ikatkov/dummy-load/ltspice/darlington-bjt-current-measurement.asc

C1: cap; 100p
Q1: npn; 2SCR583D3
Q3: npn; 2SC5866
R1: res; 1k
R2: res; 50
R3: res; 0.23
R4: res; 0.1
R5: res; 1k
R6: res; 9.1k
U1: opamp2; LM358
U2: opamp2; LM358
V1: voltage; 24
V2: voltage; 0
V3: voltage; 7
V5: voltage; {Von}; AC 0
Named nets: 0, RAW, VCC, -VCC, ref, sense, Vmes
.param Von=0.5
.inc LM358.LIB
.tran 0 100u 20u
