ikatkov/dummy-load/ltspice/PWM_example_usage.asc

X1: PWM_Gen; DutyCycle=1 PWM_V=3.3 PWM_f=50k
X2: PWM_Gen; DutyCycle={DutyCycle2} PWM_V=3.3 PWM_f=50k
X3: PWM_Gen; DutyCycle={DutyCycle3} PWM_V=PWM3_V PWM_f=PWM3_f
Named nets: my_pwm1, my_pwm2, my_pwm3
.tran 0.0005
.param DutyCycle2=40
.param DutyCycle3=75
PWM Signal Generator - Example Usage
J.Kincell June 2021
CurrentSauce.co.uk
Example 1. All parameters are set within.
i.e. Right Click component, add the PARAMS as shown here.
(Tick the check box so it apprears in sch)
Example 2. Some parameters are set within.
The duty cycle is set via an 'external' .PARAM placed within the schematic.
Allows multiple instantiations of different PWM sources
.param PWM3_V=5
.param PWM3_f=25k
Example 3. All parameters set by external .PARAM statement
When doing this, is clearer to not display the component PARAMS.
i.e. Untick the checkbox after right clicking)
Put the "PWM_Gen.asy" and "PWM_Gen.asc" in the top-level of a simulation project.
When adding a component, at the top, change the "top-level" drop-down box from the
default directory to the project directory, and there you will find the "PWM_Gen" component.
