ikatkov/dummy-load/ltspice/temp-measurement-scale.asc

R1: res; 25k
R8: res; 25k
R9: res; 5k
R10: res; 5k
U2: opamp2; LM358
V1: voltage; 7
V2: voltage; 2
V3: voltage; PWL(0 2 1m 2 2m 2.5 3m 2.5 4m 2.9)
Named nets: 0, vcc, volt-divider-scaled, v-ref
.lib LM358.lib
.tran 10m uic
