ikatkov/dummy-load/ltspice/temp-measurement.asc

R6: res; 51k
R7: res; 4.7k
R8: res; 4.7k
R9: res; 51k
R10: res; R=1k*(0.0002*temp*temp+0.0537*temp+8.5256)
R11: res; 10k
R12: res; 10k
R13: res; 10k
U2: opamp2; LM358
U3: opamp2; LM358
V1: voltage; 2
V2: voltage; 4.55
V3: voltage; 7
Named nets: 0, v-ref, vcc, volt-divider-scaled, 2V
.dc temp 0 120 1
~2.275V
2.09V ~0C
2.90V ~120C
2.09V ~0C
2.90V ~120C
.lib LM358.lib
