ikatkov/dummy-load/ltspice/voltage-measurement.asc

C1: cap; 10µ
D1: diode
D2: diode
R2: res; 25.5k
R3: res; 100k
V1: voltage; PWL(0 4 1 24 4 24 4.001 0)
V2: voltage; 5
V3: voltage; SINE(0 0.25 60)
Named nets: 0, vref, 5V
.tran 0 10 0
LSB = 23mV
10b ADC
