ikatkov/dummy-load/ltspice/LM334/LM334_test.asc

C6: cap; 100n
D1: diode; 1N4148
R1: res; 500; tol=0.1 pwr=0.1
R2: res; 5k; tol=0.1 pwr=0.1
R4: res; 10k; tol=0.001 pwr=0.010
U1: LM334
V3: voltage; 5V
Named nets: 0
.STEP TEMP  27 77
.op
Iset = 227uV*T/R1
Iset = 0.0681V/R @27°C, 300K
The LM334 should be normally used for currents >=10uA.
R2=10*R1 is recommended
for temperature compensation
