ikatkov/dummy-load/ltspice/bjt-stability-pulse.asc

C1: cap; 100p
C2: cap; 2.2µ
L1: ind; 3µ
Q1: npn; TIP122
R1: res; 10k
R2: res; 1m
R3: res; 0.23
R4: res; 0.1
R5: res; 1
U1: opamp2; LM358
V1: voltage; 5
V2: voltage; -5
V3: voltage; 5
V4: voltage; PULSE({0.001 - Von} 0 100n 100n 100n 1m); AC 0
V5: voltage; {Von}; AC 0
Named nets: 0, RAW, VCC, fb, out, -VCC, ref
;ac dec 1000 1 100Meg
.inc TLV271.LIB
.inc LM358.LIB
.tran 100u
.param Von=0.01
.lib TIP122.LIB
