ikatkov/dummy-load/ltspice/bjt-stability.asc

C2: cap; 100p
C3: cap; 2.2µ
L1: ind; 3µ
Q1: npn; 2SC5824
Q2: npn; 2N3904
R1: res; 1
R3: res; 0.23
R4: res; 100
R6: res; 10k
U1: opamp2; LM358
V1: voltage; 5
V2: voltage; -5
V3: voltage; 5
V4: voltage; ""; AC 1
V5: voltage; {Von}; AC 0
Named nets: 0, RAW, VCC, fb, -VCC, ref, inv
.ac dec 1000 1 10Meg
.inc TLV271.LIB
.inc LM358.LIB
;tran 500ms
.lib TIP122.LIB
.param Von=0.25
