ikatkov/dummy-load/ltspice/current-sense-multiplier.asc

R1: res; 1k
R2: res; 9.1k
U1: opamp2; LM358
V1: voltage; 48
V2: voltage; 7
V3: voltage; 0
V4: voltage; {Von}; AC 0
Named nets: VCC, -VCC, 0, Vmes, ref, RAW
.param Von=0.4
.inc LM358.LIB
.tran 100m
