ikatkov/dummy-load/ltspice/darlington-bjt-high-side-mes.asc

C1: cap; 220p
C2: cap; 2.2µ
L1: ind; 3µ
Q1: npn; 2SCR583D3
Q3: npn; 2SC5866
R1: res; 1k
R2: res; 47
R3: res; 1
R4: res; 0.1
R5: res; 3.3
R6: res; 10k
R7: res; 1
R8: res; 1k
R9: res; 0.215
U1: opamp2; LM358
U2: opamp2; LM358
V1: voltage; 60
V2: voltage; 0
V3: voltage; 12
V5: voltage; 2.4
V6: voltage; 8
V7: VOLTAGE; PULSE(0 30 15m 40u 40u 10m 1000)
V8: voltage; 0.2
V9: voltage; 10m
Named nets: 0, RAW, VCC, -VCC, ref, vOffset, V1, pos, neg
.inc LM358.LIB
.tran 30m
.inc TL082.LIB
on power on
when ref=0
offsets opAmp down
.inc TLV9102.LIB
