ikatkov/dummy-load/ltspice/dual-darlington-bjt-stability-pulse.asc

C1: cap; 2.2µ
C2: cap; 100p
C4: cap; 100p
L1: ind; 3µ
Q1: npn; 2SC5866
Q2: npn; 2SCR583D3
Q3: npn; 2SC5866
Q4: npn; 2SCR583D3
R1: res; 0.23
R2: res; 1k
R3: res; 1
R4: res; 50
R5: res; 0.1
R6: res; 0.23
R7: res; 1k
R9: res; 50
R10: res; 0.1
U1: opamp2; LM358
U2: opamp2; LM358
V1: voltage; 24
V2: voltage; 7
V3: voltage; 0
V4: voltage; {Von}; AC 0
V5: voltage; PULSE({0.001 - Von} 0 100n 100n 100n 1m); AC 0
Named nets: 0, RAW, VCC, -VCC, ref, V_IN
.param Von=0.25
.inc LM358.LIB
.tran 100u
