ikatkov/dummy-load/ltspice/fan-alternative.asc

D1: diode
D2: diode
M1: nmos; 2N7002
Q1: npn; 2SC2655
R1: res; 1k
R2: res; 100
R3: res; 10k
R_FAN1: res; 70
R_FAN2: res; 70
V1: voltage; 5
V4: voltage; 7
V5: voltage; PULSE(0 7 0 100n 100m 0.5m 1m)
X1: PWM_Gen; DutyCycle=90 PWM_V=5 PWM_f=980
Named nets: 0, raw, real-temp, pwm, 5V
.tran 100m
2.09V ~0C
2.90V ~120C
2.38V ~40C
2.52V ~60C
.inc tl431.lib
.param temp 25
.inc 2SC2655.lib
