ikatkov/dummy-load/ltspice/fan2.asc

D1: diode
M1: nmos; 2N7002
Q1: npn; 2N2222
R1: res; 10k
R2: res; 1k
R4: res; 33k
R5: res; 10k
R_FAN: res; 40
U1: opamp2; LM393
V1: voltage; 2.45
V2: voltage; 5
V3: voltage; 4.55
V4: voltage; 12
V5: voltage; PWL(0 2 1 3 2 2)
Named nets: 0, vcc5, real-temp, temp-ref, raw, v-ref, out
.tran 2
.lib LM393.lib
2.09V ~0C
2.90V ~120C
2.38V ~40C
2.52V ~60C
in:
+7V (raw)
+5V
GND
real-temp
b-ref
out:
fan1
fan2
