ikatkov/dummy-load/ltspice/fan3.asc

D1: diode
Q1: npn; 2N2222
R4: res; 33k
R5: res; 10k
R_FAN: res; 68
U1: opamp2; LM393
V1: voltage; 2.45
V3: voltage; 2.48
V4: voltage; 7
V5: voltage; PWL(0 2.44 2 2.46)
Named nets: 0, temp-ref, raw, temp, real-temp, out
.tran 3
.lib LM393.lib
2.09V ~0C
2.90V ~120C
2.38V ~40C
2.52V ~60C
in:
+7V (raw)
+5V
GND
real-temp
b-ref
out:
fan1
fan2
