ikatkov/dummy-load/ltspice/mosfet-stability-pulse.asc

C1: cap; 10n
L1: ind; 3µ
M1: nmos; IRFP250N
R1: res; 10k
R2: res; 620
R3: res; 0.23
R4: res; 0.1
R5: res; 100k
U1: opamp2; LM358
V1: voltage; 5
V2: voltage; -9
V3: voltage; 9
V4: voltage; PULSE({0.001 - Von} 0 1u 1u 1u 1m); AC 0
V5: voltage; {Von}; AC 0
Named nets: 0, RAW, VCC, fb, out, -VCC, ref
;ac dec 1000 1 100Meg
.inc TLV271.LIB
.inc LM358.LIB
.tran 1m
.param Von=1
