ikatkov/dummy-load/ltspice/mosfet-stability-sample.asc

C1: cap; 10n
L1: ind; 1p
M1: nmos; IRFP250N
R1: res; 10k
R2: res; 100
R3: res; 0.1
R4: res; 0.1
R5: res; 100k
U1: opamp2; LM358
V1: voltage; 15
V2: voltage; -9
V3: voltage; 9
V4: voltage; ""; AC 1
V5: voltage; 2; AC 0
Named nets: 0, RAW, VCC, fb, out, -VCC, ref, inv
.ac dec 1000 1 100Meg
.inc TLV271.LIB
.inc LM358.LIB
;tran 500ms
