ikatkov/dummy-load/ltspice/mosfet-stability.asc

D1: schottky; 1N5817
L1: ind; 1µ
M1: nmos; IPB027N10N3
M2: nmos; IRFP250N
R3: res; 1
R4: res; 0.1
U1: opamp2; LM358
U2: LT1468
V1: voltage; 15
V2: voltage; -9
V3: voltage; 9
V4: voltage; ""; AC 1
V5: voltage; 2; AC 0
Named nets: 0, RAW, VCC, fb, out, -VCC, ref, inv
.ac dec 1000 1 10Meg
.inc TLV271.LIB
.inc LM358.LIB
;tran 500ms
