ikatkov/dummy-load/ltspice/mosfet.asc

M1: nmos; IRFP250N
R1: res; 0.1
R2: res; 100
R3: res; 5.6k
R4: res; 5.6k
R6: res; 0.1
U1: opamp2; TLV271
V1: voltage; 15
V2: voltage; PULSE(0 0.1 10m 1n 1n 100m)
V3: voltage; 5
Named nets: 0, RAW, control, VCC
.tran 100ms
.inc TLV271.LIB
