ikatkov/dummy-load/ltspice/over-temp-latch2.asc

C1: cap; 10µ; Rser=4
D1: diode; 1N4148
R1: res; 10k
R2: res; 10k
R3: res; R=1k*(0.0002*temp*temp+0.0537*temp+8.5256)
R5: res; 10k
R6: res; 16.7k
R7: res; 100
U1: opamp2; LM393
V1: voltage; PWL(0 2.1 1 3 2 2.1)
V2: voltage; 5
V3: voltage; 4.55
Named nets: 0, vcc5, real-temp, v-ref, over-temp-sig, th
.lib LM393.lib
PTC
.tran 2.5 startup
2.85V ~110C
over temp is LOW
