ikatkov/dummy-load/ltspice/power-resistor-trim.asc

R1: res; 1.05
R2: res; 22
V1: voltage; 1
Named nets: 0
.tran 100u
