ikatkov/dummy-load/ltspice/pwm.asc

C1: cap; 1µ
C2: cap; 1µ
C3: cap; 1µ
M1: nmos; 2N7002
R1: res; 100
R2: res; 1k
R3: res; 100
R4: res; 100
R5: res; 100
V1: voltage; 4.55
X1: PWM_Gen; DutyCycle=50 PWM_V=5 PWM_f=8k
Named nets: pwm, 0, out1, out2, out3
.tran 100m
