ikatkov/dummy-load/ltspice/PWM_Gen.asc

A1: schmitt; Vt={{100-DutyCycle}/100} Vh=0 Vhigh={PWM_V} Vlow=0 Trise=0
V2: signal; PULSE(0 1 0 {0.999/PWM_f} {0.001/PWM_f} 0 {1/PWM_f})
Named nets: 0, Vpwm
PWM Signal Generator Circuit
J.Kincell June 2021
CurrentSauce.co.uk
