ikatkov/dummy-load/ltspice/TL431-high-current.asc

I1: current; 10m
Q2: npn; 2N3904
R1: res; 60
R2: res; 3.32k
R3: res; 2.74k
R4: res; 100
R5: res; 2k
R6: res; 1m
R_LOAD: res; 50
U1: tl431
U2: opamp2; LM358
V1: voltage; PWL(0 6 1 12)
V2: voltage; 1
V3: voltage; 0
V4: voltage; 6.9
Named nets: 0, -VCC, ref, RAW
.tran 0 10 0
.include tl431.lib
4.55V
~10mA available
.inc LM358.LIB
