ikatkov/dummy-load/ltspice/TL431ref1.asc

R1: res; 470
R2: res; 3.32k
R3: res; 2.74k
R4: res; 4k
U1: tl431
V1: voltage; PWL(0 6 1 12)
Named nets: 0, vref
.tran 0 10 0
.include tl431.lib
4.55V
~10mA available
