ikatkov/dummy-load/ltspice/fan.asc

D1: diode
M1: nmos; 2N7002
R1: res; 7.5k
R2: res; 1k
R3: res; R=1k*(0.0002*temp*temp+0.0537*temp+8.5256)
R4: res; 25k
R5: res; 1k
R_FAN: res; 40
U1: opamp2; LM393
V1: voltage; 1.75
V2: voltage; 5
V3: voltage; 4.55
V4: voltage; 7
Named nets: 0, vcc5, v-temp, temp-ref, raw, v-ref
.dc temp 1 120 1
.lib LM393.lib
1.69V on ~62C
1.85V off ~35C
