ikatkov/dummy-load/ltspice/over-temp-latch.asc

M1: nmos; 2N7002
M2: nmos; 2N7002
R1: res; 7.5k
R2: res; 10k
R3: res; R=1k*(0.0002*temp*temp+0.0537*temp+8.5256)
R4: res; 10k
R5: res; 10k
R6: res; 4.42k
U1: opamp2; LM393
V1: voltage; PWL(0 2.1 1 1.3 2 2.1)
V2: voltage; 5
V3: voltage; 4.55
Named nets: 0, vcc5, v-temp, v-ref, over-temp-sig, ~over-temp-sig
.tran 2.5 startup
.lib LM393.lib
1.4V ~110C
