ikatkov/dummy-load/kicad/all/all.kicad_sch

## KiCad design kicad/all/all.kicad_sch (2024-02-22)

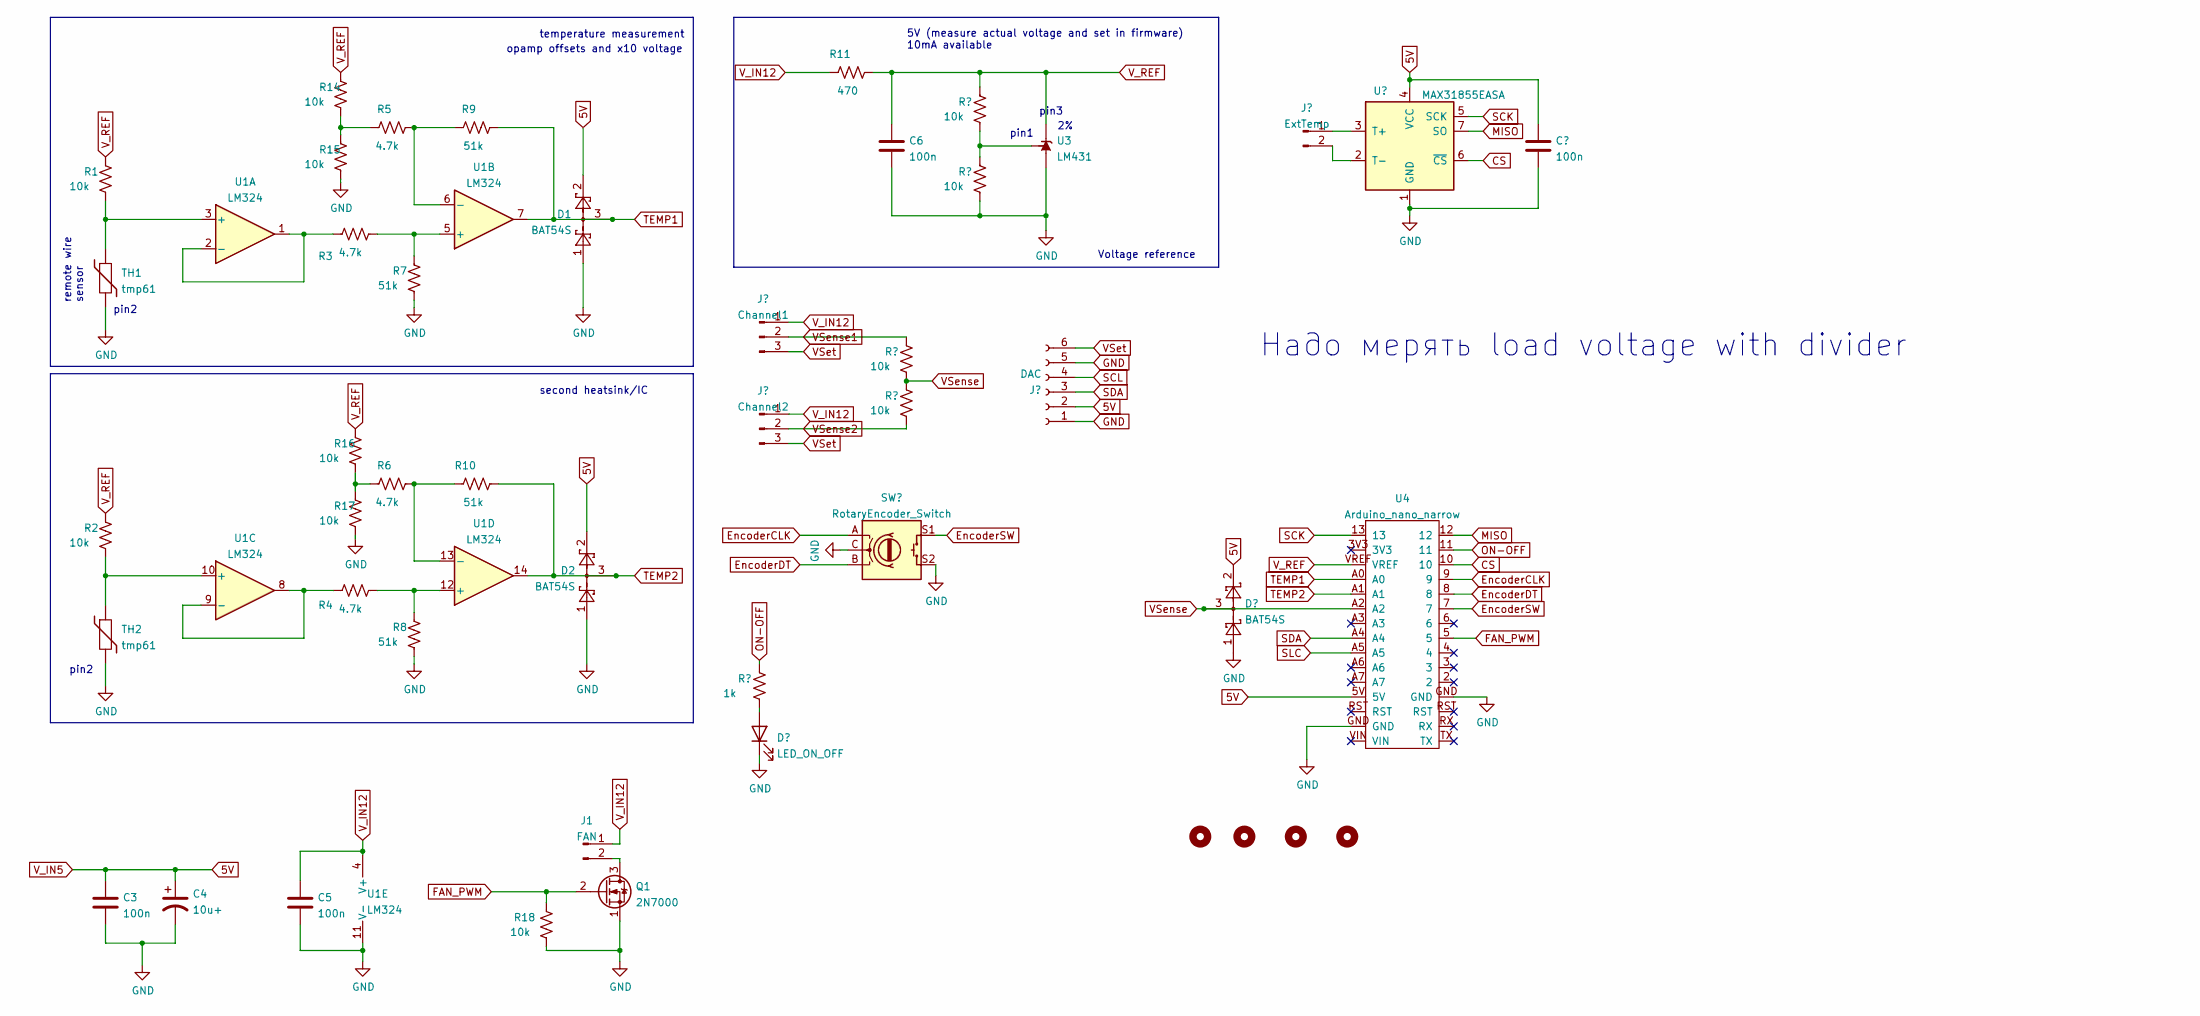
[picture p9: schematic all.kicad_sch]

Parts:
C3, C5, C6: 100n
C4: 10u+
D1, D2: BAT54S; SOT-23
H1, H2, H3, H4: MountingHole; MountingHole_3.2mm_M3
J1: FAN
Q1: 2N7000; TO-92_Inline
R1, R2, R14, R15, R16, R17, R18: 10k; R_1206_3216Metric_Pad1.30x1.75mm_HandSolder
R3, R4, R5, R6: 4.7k; R_1206_3216Metric_Pad1.30x1.75mm_HandSolder
R7, R8, R9, R10: 51k; R_1206_3216Metric_Pad1.30x1.75mm_HandSolder
R11: 470; R_1206_3216Metric_Pad1.30x1.75mm_HandSolder
TH1, TH2: tmp61; JST_XH_B2B-XH-AM_1x02_P2.50mm_Vertical
U1: LM324
U3: LM431; TO-92L_HandSolder
U4: Arduino_nano_narrow; ARDUINO_NANO_NARROW

Connections:
5V: C3.1, C4.1, D1.2, D2.2, U4.5V
CS: U4.10
EncoderCLK: U4.9
EncoderDT: U4.8
EncoderSW: U4.7
FAN_PWM: Q1.2 (G), R18.1, U4.5
GND: C3.2, C4.2, C5.2, C6.2, D1.1, D2.1, Q1.1 (S), R7.2, R8.2, R15.2, R17.2, R18.2, TH1.2, TH2.2, U1.11 (V-), U3.2 (A), U4.GND
MISO: U4.12
unnamed: J1.2, Q1.3 (D)
unnamed: R1.2, TH1.1, U1.3 (+)
unnamed: R2.2, TH2.1, U1.10 (+)
unnamed: R3.1, U1.1, U1.2 (-)
unnamed: R3.2, R7.1, U1.5 (+)
unnamed: R4.1, U1.8, U1.9 (-)
unnamed: R4.2, R8.1, U1.12 (+)
unnamed: R5.2, R9.1, U1.6 (-)
unnamed: R6.2, R10.1, U1.13 (-)
unnamed: R5.1, R14.2, R15.1
unnamed: R6.1, R16.2, R17.1
ON-OFF: U4.11
SCK: U4.13
SDA: U4.A4
SLC: U4.A5
TEMP1: D1.3, R9.2, U1.7, U4.A0
TEMP2: D2.3, R10.2, U1.14, U4.A1
VSense: U4.A2
V_IN12: C5.1, J1.1, R11.1, U1.4 (V+)
V_REF: C6.1, R1.1, R2.1, R11.2, R14.1, R16.1, U3.3 (K), U4.VREF

Notes on the sheet:
remote wire sensor
pin3
5V (measure actual voltage and set in firmware) 10mA available
pin1
opamp offsets and x10 voltage
Voltage reference
second heatsink/IC
Надо мерять load voltage with divider
pin2
temperature measurement
