ikatkov/dummy-load/kicad/current-control/current-control.kicad_sch

## KiCad design kicad/current-control/current-control.kicad_sch (2024-02-22)

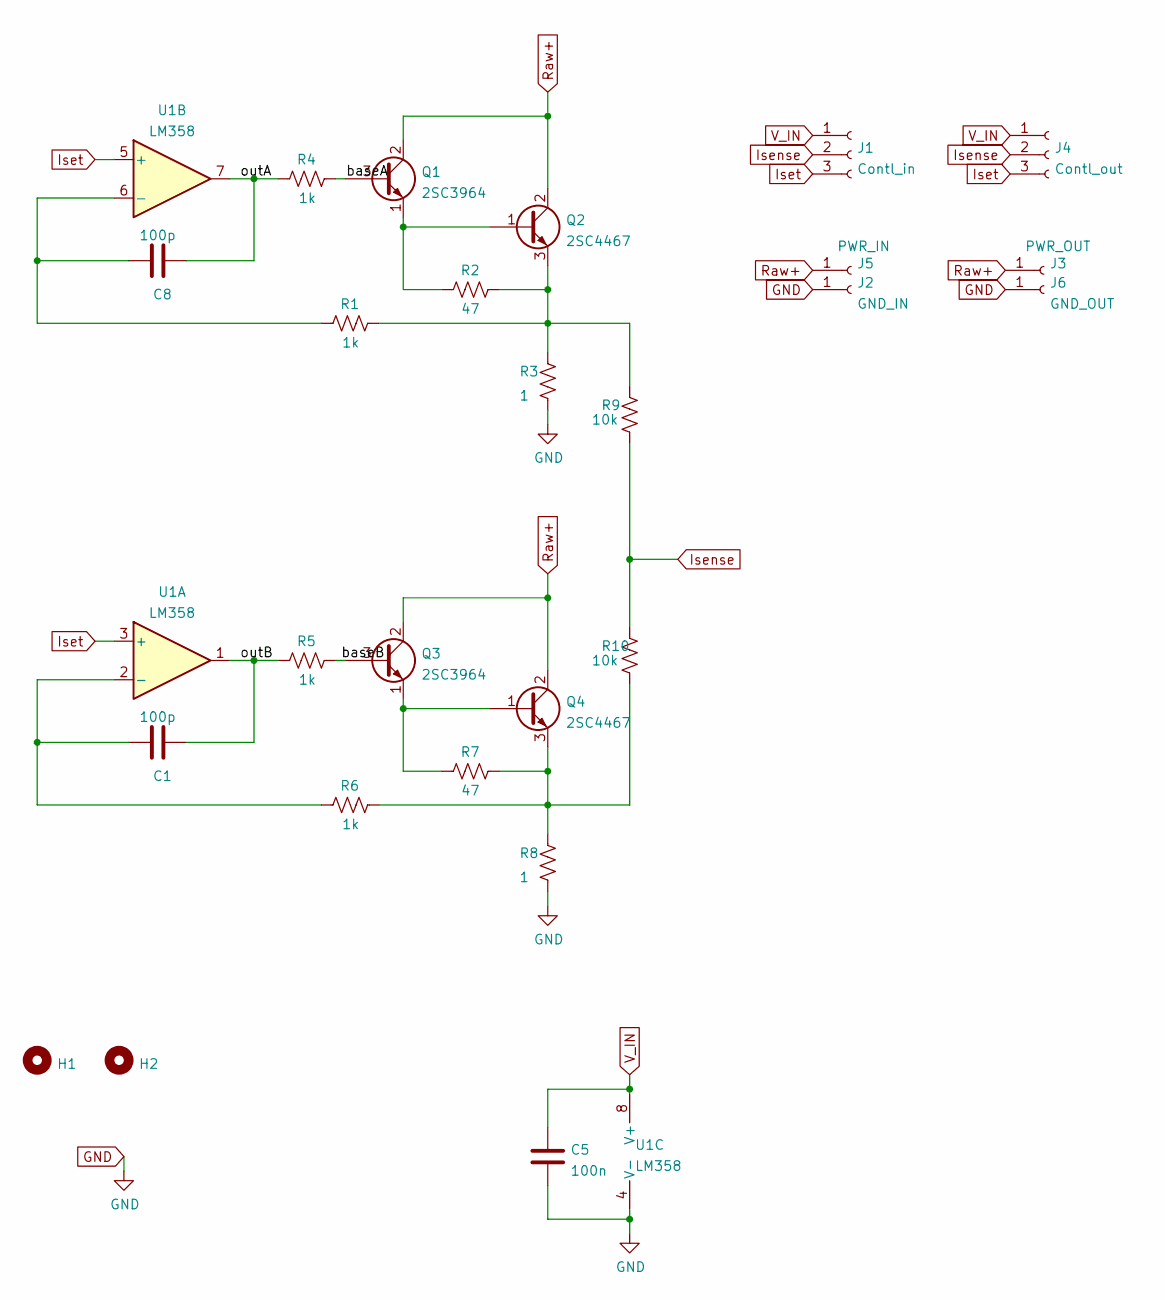
[picture p10: schematic current-control.kicad_sch]

Parts:
C1, C8: 100p; C_1206_3216Metric
C5: 100n; C_1206_3216Metric
H1, H2: MountingHole; MountingHole_3.2mm_M3
J1: Contl_in; PinSocket_1x03_P2.54mm_Vertical
J2: GND_IN; SolderWire-1.5sqmm_1x01_D1.7mm_OD3mm
J3: PWR_OUT; SolderWire-1.5sqmm_1x01_D1.7mm_OD3mm
J4: Contl_out; PinSocket_1x03_P2.54mm_Vertical
J5: PWR_IN; SolderWire-1.5sqmm_1x01_D1.7mm_OD3mm
J6: GND_OUT; SolderWire-1.5sqmm_1x01_D1.7mm_OD3mm
Q1, Q3: 2SC3964; TO-126-3_Vertical
Q2, Q4: 2SC4467; TO-3P-3_Vertical
R1, R4: 1k; R_1206_3216Metric
R2, R7: 47; R_0805_2012Metric
R3, R8: 1; R_Axial_Power_L25.0mm_W9.0mm_P30.48mm
R5, R6: 1k; R_0805_2012Metric
R9, R10: 10k; R_0805_2012Metric
U1: LM358; SOIC-8_3.9x4.9mm_P1.27mm

Connections:
GND: C5.2, J2.1, J6.1, R3.2, R8.2, U1.4 (V-)
Isense: J1.2, J4.2, R9.2, R10.1
Iset: J1.3, J4.3, U1.3 (+), U1.5 (+)
unnamed: C1.1, R6.1, U1.2 (-)
unnamed: C8.1, R1.1, U1.6 (-)
unnamed: Q1.1 (E), Q2.1 (B), R2.1
unnamed: Q2.3 (E), R1.2, R2.2, R3.1, R9.1
unnamed: Q3.1 (E), Q4.1 (B), R7.1
unnamed: Q4.3 (E), R6.2, R7.2, R8.1, R10.2
Raw+: J3.1, J5.1, Q1.2 (C), Q2.2 (C), Q3.2 (C), Q4.2 (C)
V_IN: C5.1, J1.1, J4.1, U1.8 (V+)
baseA: Q1.3 (B), R4.2
baseB: Q3.3 (B), R5.2
outA: C8.2, R4.1, U1.7
outB: C1.2, R5.1, U1.1
