ikatkov/dummy-load/kicad/temp-measurements/temp-measurements.kicad_sch

## KiCad design kicad/temp-measurements/temp-measurements.kicad_sch (2024-02-22, an earlier design)

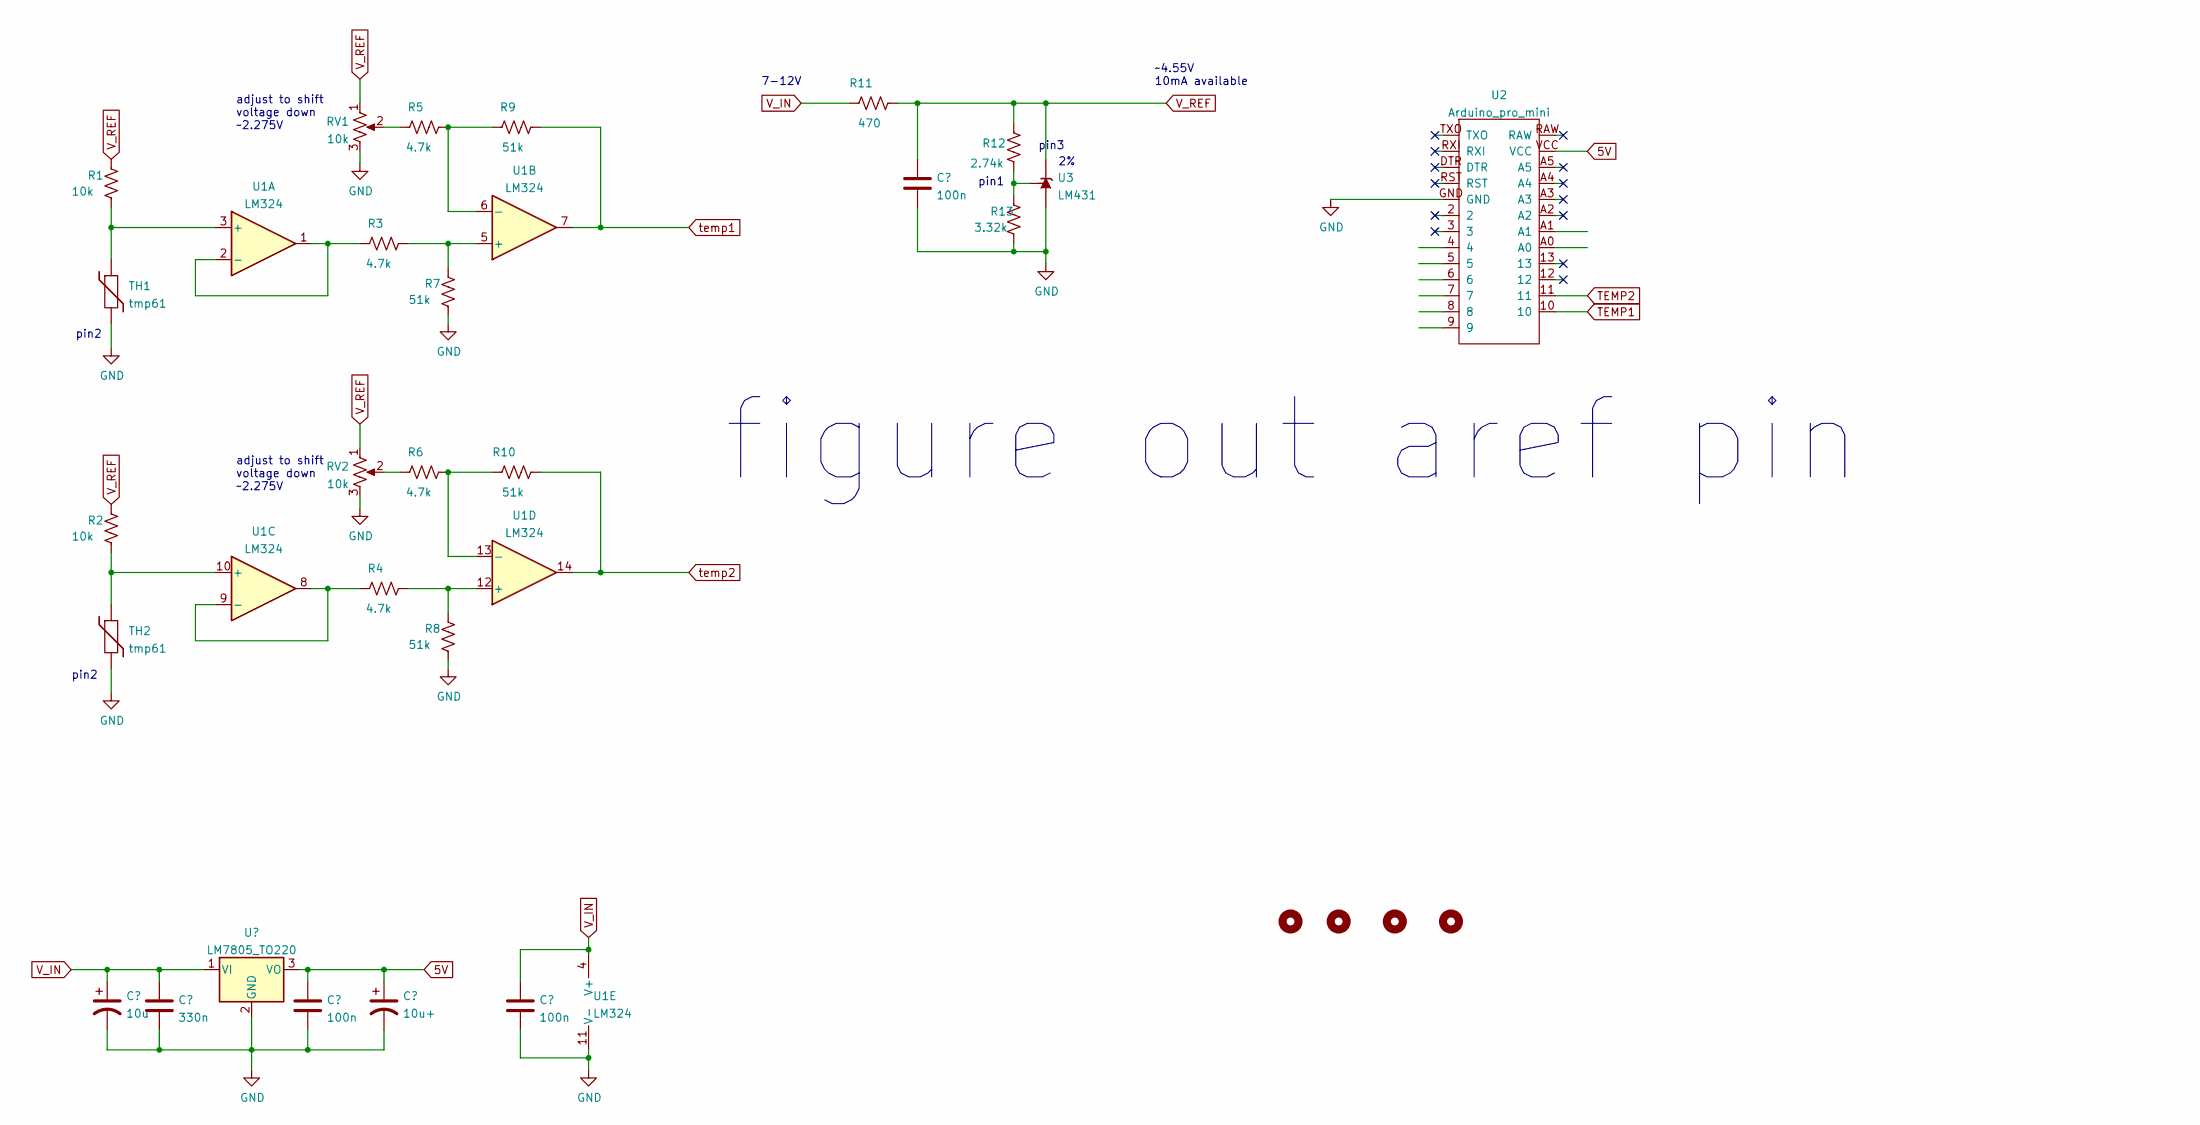
[picture p11: schematic temp-measurements.kicad_sch]

Parts:
H1, H2, H3, H4: MountingHole; MountingHole_3.2mm_M3
R1, R2: 10k; R_1206_3216Metric_Pad1.30x1.75mm_HandSolder
R3, R4, R5, R6: 4.7k; R_1206_3216Metric_Pad1.30x1.75mm_HandSolder
R7, R8, R9, R10: 51k; R_1206_3216Metric_Pad1.30x1.75mm_HandSolder
R11: 470; R_1206_3216Metric_Pad1.30x1.75mm_HandSolder
R12: 2.74k; R_1206_3216Metric_Pad1.30x1.75mm_HandSolder
R13: 3.32k; R_1206_3216Metric_Pad1.30x1.75mm_HandSolder
RV1, RV2: 10k
TH1, TH2: tmp61; JST_XH_B2B-XH-AM_1x02_P2.50mm_Vertical
U1: LM324
U2: Arduino_pro_mini; ARDUINO_PRO_MINI_NO_A5
U3: LM431; TO-92L_HandSolder

Connections:
5V: U2.VCC
GND: R7.2, R8.2, R13.2, RV1.3, RV2.3, TH1.2, TH2.2, U1.11 (V-), U2.GND, U3.2 (A)
unnamed: R1.2, TH1.1, U1.3 (+)
unnamed: R2.2, TH2.1, U1.10 (+)
unnamed: R3.1, U1.1, U1.2 (-)
unnamed: R3.2, R7.1, U1.5 (+)
unnamed: R4.1, U1.8, U1.9 (-)
unnamed: R4.2, R8.1, U1.12 (+)
unnamed: R5.1, RV1.2
unnamed: R5.2, R9.1, U1.6 (-)
unnamed: R6.1, RV2.2
unnamed: R6.2, R10.1, U1.13 (-)
unnamed: R12.2, R13.1, U3.1 (REF)
V_IN: R11.1, U1.4 (V+)
V_REF: R1.1, R2.1, R11.2, R12.1, RV1.1, RV2.1, U3.3 (K)
temp1: R9.2, U1.7, U2.10
temp2: R10.2, U1.14, U2.11

Notes on the sheet:
adjust to shift voltage down ~2.275V
pin3
~4.55V 10mA available
pin1
figure out aref pin
7-12V
pin2
